LennartEd/Analog-Keyboard-kmk-PiPico-NormalSplit/Split/Code/hallCali.py

input_range =[
[44298, 176], [44842, 176], [45851, 304], [45451, 176], [45211, 160], [44970, 176], [44762, 4353], [45963, 2000], [46379, 4609], [45771, 256], [45483, 3216], [45531, 176], [44346, 160], [44682, 176], [45018, 160], [45018, 160],[46079,5904],[45701,2883],[45221,138],[45392,136],[44981,140],[45142,137],
[0,0],[0,0],[0,0],[0,0],[0,0],
[47364,304],[47615,304],[47571,2601],[47265,302],[47518,302],[47226,302],[47760,303],[47089,302],[46675,303],[47663,3700],[47896,1953],[47265,301],[47698,304],[47328,1208],[47873,2720],[47780,301],[47790, 802],[47638,340],[47900,1568],[47042,303],[47046,304],[46847,304]
]
output_range = (0,4)
